Bertruss/MM-Macro-Pad/Hardware Design/Circuit Design/Key Matrix with LEDs.asc

D1: diode
D2: diode
D3: diode
D4: diode
D5: diode
D6: diode
D7: diode
D8: diode
D9: diode
D10: LED
D11: LED
D12: LED
D13: LED
D14: LED
D15: LED
D16: LED
D17: LED
D18: LED
R1: res; 5K
R2: res; 5K
R3: res; 5K
R4: res; 250
R5: res; 250
R6: res; 250
S1: sw
S2: sw
S3: sw
S4: sw
S5: sw
S6: sw
S7: sw
S8: sw
S9: sw
U1: DIP20
Named nets: 0
