Bertruss/MM-Macro-Pad/Hardware Design/Circuit Design/Key Matrix.asc

D1: diode
D2: diode
D3: diode
D4: diode
D5: diode
D6: diode
D7: diode
D8: diode
D9: diode
R1: res; 5K
R2: res; 5K
R3: res; 5K
S1: sw
S2: sw
S3: sw
S4: sw
S5: sw
S6: sw
S7: sw
S8: sw
S9: sw
U1: DIP20
Named nets: 0
Teensy LC
